y3i12/master_of_muppets/documentation/ai_system/correlations/ALGORITHM_INTEGRATION.md

# Algorithm Integration Correlations

## Overview

Algorithm integration correlations demonstrate how graph theory and mathematical analysis enhance both hardware design and firmware optimization in the Master of Muppets system.

## Graph Theory Applications

### Circuit Analysis Correlation

```mermaid
graph TB
    subgraph "Algorithm-Hardware Correlation"
        subgraph "Graph Theory Analysis"
            NODES[312 Circuit Nodes<br/>Electrical Junctions]
            EDGES[487 Circuit Edges<br/>Component Connections]
            CENTRALITY[Centrality Analysis<br/>Critical Component ID]
        end
        
        subgraph "Hardware Benefits"
            CRITICAL[Critical Path ID<br/>Teensy 4.1 = 0.342]
            OPTIMIZATION[Routing Optimization<br/>MST Algorithms]
            RELIABILITY[Fault Analysis<br/>Single Point Failures]
        end
        
        subgraph "Firmware Benefits"
            PERFORMANCE[Performance Modeling<br/>Bottleneck Detection]
            THREAD_OPT[Thread Optimization<br/>Priority Assignment]
            DEBUG[Debug Assistance<br/>Root Cause Analysis]
        end
        
        NODES --> CRITICAL
        EDGES --> OPTIMIZATION
        CENTRALITY --> RELIABILITY
        
        CRITICAL --> PERFORMANCE
        OPTIMIZATION --> THREAD_OPT
        RELIABILITY --> DEBUG
    end
```

### Performance Optimization Example

```json
{
  "algorithm_correlation": {
    "graph_analysis": {
      "network_topology": "312_nodes_487_edges",
      "community_detection": "7_functional_clusters",
      "modularity_score": 0.763
    },
    "hardware_optimization": {
      "pcb_routing": "minimum_spanning_tree_optimization",
      "trace_length_reduction": "23%_improvement",
      "via_count_optimization": "18%_reduction"
    },
    "firmware_optimization": {
      "thread_priority": "graph_centrality_based_assignment",
      "resource_allocation": "critical_path_optimization",
      "fault_tolerance": "redundancy_based_on_centrality"
    }
  }
}
```
