y3i12/master_of_muppets/documentation/ai_system/correlations/CROSS_DOMAIN_CORRELATIONS.md

# Cross-Domain Correlations

## Overview

Cross-domain correlations represent the breakthrough innovation of the Master of Muppets project - the ability to systematically analyze and optimize relationships between hardware, firmware, algorithms, and manufacturing domains. This capability has enabled unprecedented system-level optimization and validation.

## Correlation Architecture

```mermaid
graph TB
    subgraph "Cross-Domain Correlation System"
        subgraph "Knowledge Domains"
            HW[Hardware Domain<br/>Schematics, Components, PCB]
            FW[Firmware Domain<br/>Code, Threading, Drivers]
            ALG[Algorithm Domain<br/>Graph Theory, Analysis]
            MFG[Manufacturing Domain<br/>Production, Testing, QA]
        end
        
        subgraph "Correlation Engine"
            MAPPER[Relationship Mapper<br/>Domain Interfaces]
            ANALYZER[Correlation Analyzer<br/>Constraint Validation]
            OPTIMIZER[System Optimizer<br/>Performance Enhancement]
            VALIDATOR[Design Validator<br/>Consistency Checking]
        end
        
        subgraph "Correlation Outputs"
            INSIGHTS[System Insights<br/>Optimization Opportunities]
            VALIDATION[Design Validation<br/>Multi-domain Consistency]
            PREDICTION[Performance Prediction<br/>System Modeling]
            OPTIMIZATION[Automated Optimization<br/>Improvement Suggestions]
        end
        
        HW --> MAPPER
        FW --> MAPPER
        ALG --> MAPPER
        MFG --> MAPPER
        
        MAPPER --> ANALYZER
        ANALYZER --> OPTIMIZER
        OPTIMIZER --> VALIDATOR
        
        ANALYZER --> INSIGHTS
        OPTIMIZER --> VALIDATION
        VALIDATOR --> PREDICTION
        MAPPER --> OPTIMIZATION
    end
```

## Correlation Methodology

### Domain Interface Mapping

```mermaid
graph LR
    subgraph "Domain Interface Identification"
        HW_CONSTRAINTS[Hardware Constraints<br/>Timing, Power, Thermal]
        FW_REQUIREMENTS[Firmware Requirements<br/>Memory, Performance, Timing]
        ALG_DEMANDS[Algorithm Demands<br/>Processing, Complexity]
        MFG_LIMITS[Manufacturing Limits<br/>Tolerances, Assembly]
        
        INTERFACE[Interface Points<br/>Cross-Domain Connections]
        
        HW_CONSTRAINTS --> INTERFACE
        FW_REQUIREMENTS --> INTERFACE
        ALG_DEMANDS --> INTERFACE
        MFG_LIMITS --> INTERFACE
    end
```

This represents a revolutionary approach to system design where all engineering domains are analyzed simultaneously for optimization opportunities and constraint validation.
