y3i12/master_of_muppets/firmware/src/master_of_muppets.hpp

#pragma once

#include "dr_teeth.h"

uint16_t                     dr_teeth::input_buffer[ dr_teeth::k_total_channels ]   = { 0 };
uint16_t                    dr_teeth::output_buffer[ dr_teeth::k_total_channels ]   = { 0 };
